Electro707/OSLB56317_Driver/Firmware_FFT/misc_tools/test_dsp.py

import matplotlib.pyplot as plt
import numpy as np
import scipy.fft as fft

fft_size = 512
fs = 48000

fc = 1000
fc2 = 500

x = np.arange(0, fft_size/fs, (1/fs))
# y = np.sin(fc*2*np.pi * x)
y = [0,3849,7632,11285,14745,17953,20853,23396,25540,27246,28486,29238,29491,29238,28486,27246,25540,23396,20853,17953,14745,11285,7632,3849,0,-3849,-7632,-11285,-14745,-17953,-20853,-23396,-25540,-27246,-28486,-29238,-29491,-29238,-28486,-27246,-25540,-23396,-20853,-17953,-14745,-11285,-7632,-3849,0,3849,7632,11285,14745,17953,20853,23396,25540,27246,28486,29238,29491,29238,28486,27246,25540,23396,20853,17953,14745,11285,7632,3849,0,-3849,-7632,-11285,-14745,-17953,-20853,-23396,-25540,-27246,-28486,-29238,-29491,-29238,-28486,-27246,-25540,-23396,-20853,-17953,-14745,-11285,-7632,-3849,0,3849,7632,11285,14745,17953,20853,23396,25540,27246,28486,29238,29491,29238,28486,27246,25540,23396,20853,17953,14745,11285,7632,3849,0,-3849,-7632,-11285,-14745,-17953,-20853,-23396,-25540,-27246,-28486,-29238,-29491,-29238,-28486,-27246,-25540,-23396,-20853,-17953,-14745,-11285,-7632,-3849,0,3849,7632,11285,14745,17953,20853,23396,25540,27246,28486,29238,29491,29238,28486,27246,25540,23396,20853,17953,14745,11285,7632,3849,0,-3849,-7632,-11285,-14745,-17953,-20853,-23396,-25540,-27246,-28486,-29238,-29491,-29238,-28486,-27246,-25540,-23396,-20853,-17953,-14745,-11285,-7632,-3849,0,3849,7632,11285,14745,17953,20853,23396,25540,27246,28486,29238,29491,29238,28486,27246,25540,23396,20853,17953,14745,11285,7632,3849,0,-3849,-7632,-11285,-14745,-17953,-20853,-23396,-25540,-27246,-28486,-29238,-29491,-29238,-28486,-27246,-25540,-23396,-20853,-17953,-14745,-11285,-7632,-3849,0,3849,7632,11285,14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

x = x[1:(fft_size//2)]
y_fft = y_fft[1:(fft_size//2)]

plt.plot(x, (y_fft.real*y_fft.real) / 2**16)
plt.plot(x, (y_fft.imag*y_fft.imag) / 2**16)
plt.show()

y2 = (y_fft.imag*y_fft.imag) + (y_fft.real*y_fft.real)
y2 /= 2**16
plt.plot(x, y2)
plt.show()
